FOSSEE/OpenPLC/OpenPLC_Atmega16/assets/openplc.png

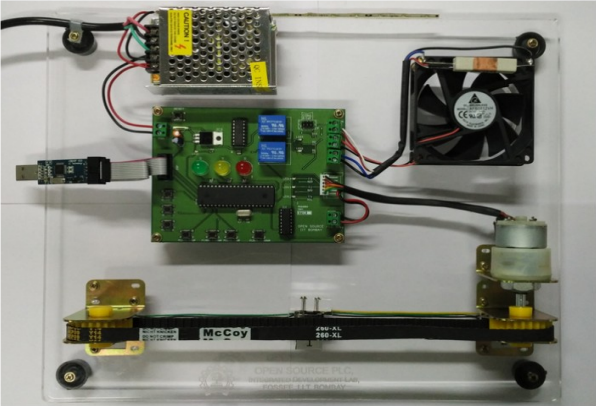
OpenPLC_Atmega16/assets/openplc.png
