FOSSEE/OpenPLC/OpenPLC_Atmega16/software/SoftImages/ldmicro.png

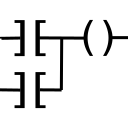
OpenPLC_Atmega16/software/SoftImages/ldmicro.png
