FOSSEE/OpenPLC/Resources/OpenPLCVersion1/OpenPLC.sch

## EAGLE design Resources/OpenPLCVersion1/OpenPLC.sch (2016-04-25)

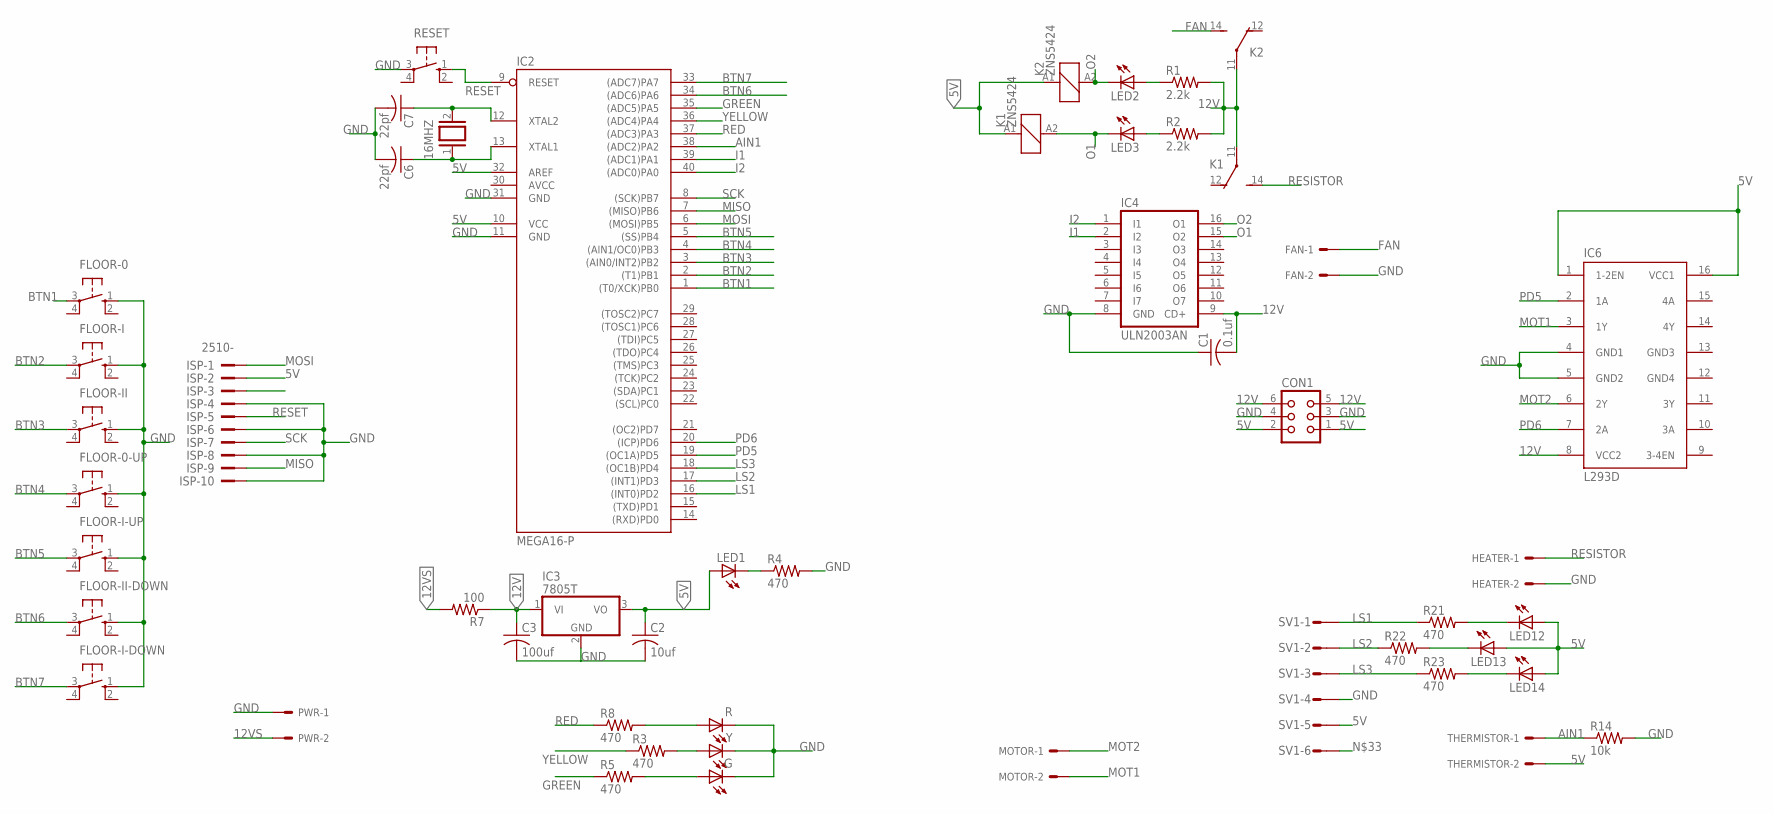
[picture p41: schematic OpenPLC.sch]

Parts:
16MHZ: XTAL/S; QS
C1: 0.1uf; C0805
C2: 10uf; C025-025X050
C3: 100uf; C025-025X050
C6, C7: 22pf; C0805
CON1: CON06
FAN: KK-156-2
FLOOR-0, FLOOR-0-UP: 10-XX; B3F-10XX
FLOOR-I: 10-XX; B3F-10XX
FLOOR-I-DOWN: 10-XX; B3F-10XX
FLOOR-I-UP: 10-XX; B3F-10XX
FLOOR-II: 10-XX; B3F-10XX
FLOOR-II-DOWN: 10-XX; B3F-10XX
G: LED10MM
HEATER: KK-156-2
IC2: MEGA16-P; DIL40
IC3: 7805T; TO220H
IC4: ULN2003AN; DIL16
IC6: L293D; DIL16
ISP: 2510-; PAK100/2500-10
K1, K2: ZNS5424; ZN5
LED1, LED2, LED3, LED12, LED13, LED14: LEDSML0805; SML0805
MOTOR: KK-156-2
PWR: KK-156-2
R: LED10MM
R1, R2: 2.2k; R0805
R3, R4, R5, R8, R21, R22, R23: 470; R0805
R7: 100; 0207/12
R14: 10k; R0805
RESET: 10-XX; B3F-10XX
SV1: L06P
THERMISTOR: KK-156-2
Y: LED10MM

Connections:
5V: C2.1, CON1.1, CON1.2, IC2.10 (VCC), IC2.32 (AREF), IC3.3 (VO), IC6.1 (1-2EN), IC6.16 (VCC1), ISP.2, K1.A1 (1), K2.A1 (1), LED1.A, LED12.A, LED13.A, LED14.A, SV1.5, THERMISTOR.2
12V: C1.2, C3.1, CON1.5, CON1.6, IC3.1 (VI), IC4.9 (CD+), IC6.8 (VCC2), K1.11, K2.11, R1.2, R2.2, R7.1
12VS: PWR.2, R7.2
AIN1: IC2.38 ((ADC2)PA2), R14.1, THERMISTOR.1
BTN1: FLOOR-0.3, IC2.1 ((T0/XCK)PB0)
BTN2: FLOOR-I.3, IC2.2 ((T1)PB1)
BTN3: FLOOR-II.3, IC2.3 ((AIN0/INT2)PB2)
BTN4: FLOOR-0-UP.3, IC2.4 ((AIN1/OC0)PB3)
BTN5: FLOOR-I-UP.3, IC2.5 ((SS)PB4)
BTN6: FLOOR-II-DOWN.3, IC2.34 ((ADC6)PA6)
BTN7: FLOOR-I-DOWN.3, IC2.33 ((ADC7)PA7)
FAN: FAN.1, K2.14 (S)
G: G.A, R5.2
GND: C1.1, C2.2, C3.2, C6.2, C7.2, CON1.3, CON1.4, FAN.2, FLOOR-0.1 (S), FLOOR-0-UP.1 (S), FLOOR-I.1 (S), FLOOR-I-DOWN.1 (S), FLOOR-I-UP.1 (S), FLOOR-II.1 (S), FLOOR-II-DOWN.1 (S), G.K (C), HEATER.2, IC2.11 (GND), IC2.31 (GND), IC3.2 (GND), IC4.8 (GND), IC6.4 (GND1), IC6.5 (GND2), ISP.4, ISP.6, ISP.8, ISP.10, PWR.1, R.K (C), R4.2, R14.2, RESET.3, SV1.4, Y.K (C)
GREEN: IC2.35 ((ADC5)PA5), R5.1
I1: IC2.39 ((ADC1)PA1), IC4.2 (I2)
I2: IC2.40 ((ADC0)PA0), IC4.1 (I1)
LS1: IC2.16 ((INT0)PD2), R21.1, SV1.1
LS2: IC2.17 ((INT1)PD3), R22.1, SV1.2
LS3: IC2.18 ((OC1B)PD4), R23.1, SV1.3
MISO: IC2.7 ((MISO)PB6), ISP.9
MOSI: IC2.6 ((MOSI)PB5), ISP.1
MOT1: IC6.3 (1Y), MOTOR.2
MOT2: IC6.6 (2Y), MOTOR.1
unnamed: LED1.C, R4.1
unnamed: LED2.A, R1.1
unnamed: LED3.A, R2.1
unnamed: LED12.C, R21.2
unnamed: LED13.C, R22.2
unnamed: LED14.C, R23.2
unnamed: 16MHZ.1, C6.1, IC2.13 (XTAL1)
unnamed: 16MHZ.2, C7.1, IC2.12 (XTAL2)
O1: IC4.15 (O2), K1.A2 (2), LED3.C
O2: IC4.16 (O1), K2.A2 (2), LED2.C
PD5: IC2.19 ((OC1A)PD5), IC6.2 (1A)
PD6: IC2.20 ((ICP)PD6), IC6.7 (2A)
R: R.A, R8.2
RED: IC2.37 ((ADC3)PA3), R8.1
RESET: IC2.9 (RESET), ISP.5, RESET.1 (S)
RESISTOR: HEATER.1, K1.14 (S)
SCK: IC2.8 ((SCK)PB7), ISP.7
Y: R3.2, Y.A
YELLOW: IC2.36 ((ADC4)PA4), R3.1
