FOSSEE/OpenPLC/Resources/OpenPLCVersion1/KiCAD_Files/OpenPLC_Kicad.sch

## KiCad design Resources/OpenPLCVersion1/KiCAD_Files/OpenPLC_Kicad.sch (2017-04-03)

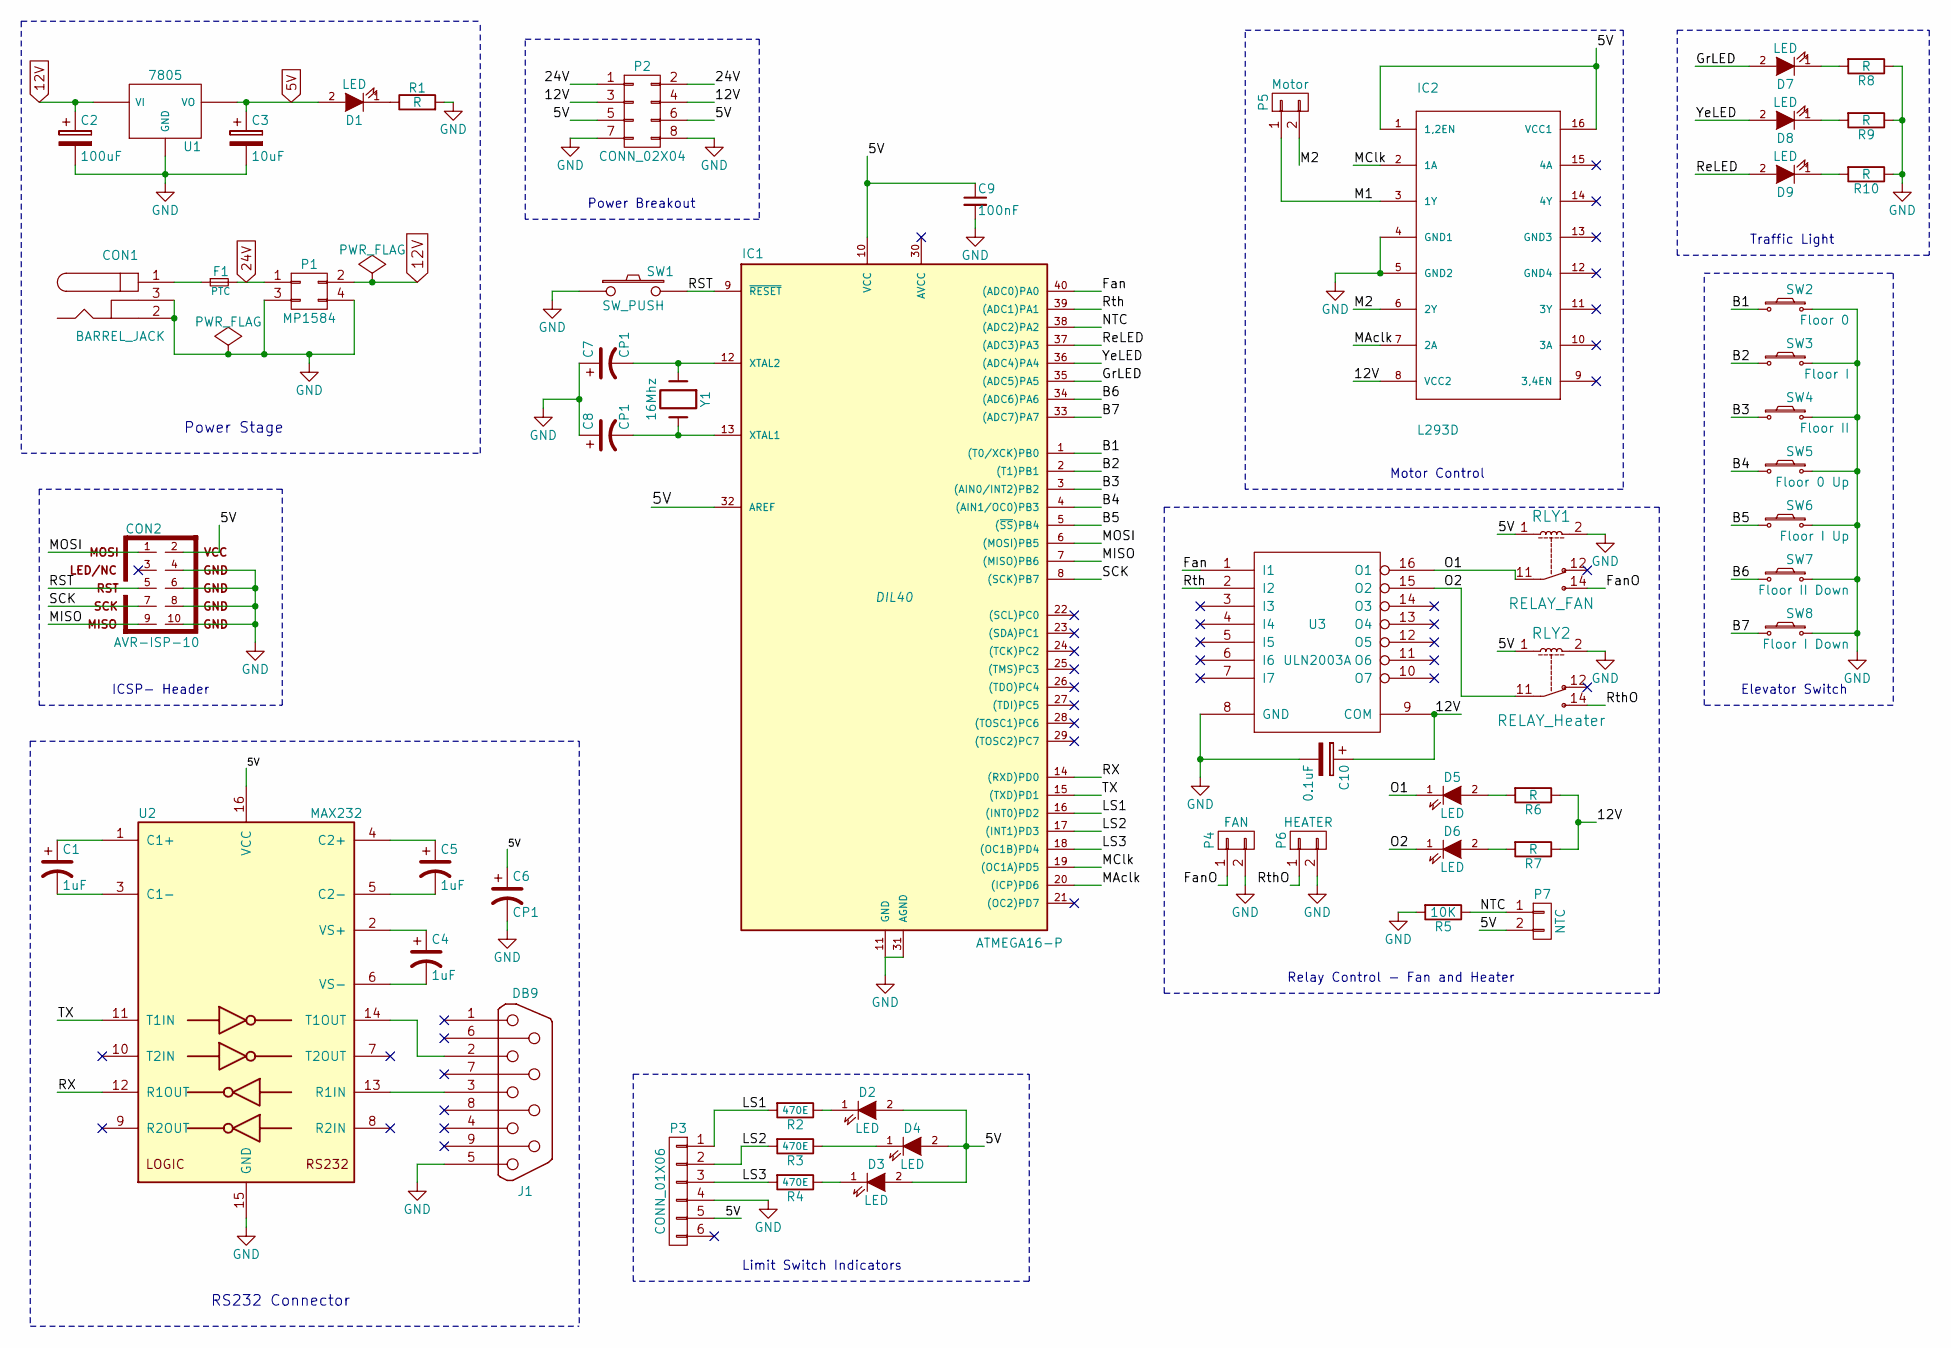
[picture p42: schematic OpenPLC_Kicad.sch]

Parts:
C1, C4, C5: 1uF
C2: 100uF
C3: 10uF
C6, C7, C8: CP1
C9: 100nF
C10: 0.1uF
CON1: BARREL_JACK
CON2: AVR-ISP-10
D1, D2, D3, D4, D5, D6, D7, D8, D9: LED
F1: PTC
IC1: ATMEGA16-P; DIL40
IC2: L293D; stepper drivers-DIL16
J1: DB9
P1: MP1584
P2: CONN_02X04
P3: CONN_01X06
P4: FAN
P5: Motor
P6: HEATER
P7: NTC
R1, R6, R7, R8, R9, R10: R
R2, R3, R4: 470E
R5: 10K
RLY1: RELAY_FAN
RLY2: RELAY_Heater
SW1: SW_PUSH
SW2: Floor 0
SW3: Floor I
SW4: Floor II
SW5: Floor 0 Up
SW6: Floor I Up
SW7: Floor II Down
SW8: Floor I Down
U1: 7805
U2: MAX232
U3: ULN2003A
Y1: 16Mhz

Connections:
5V: C3.1, C6.1, C9.1, CON2.2, D1.2 (A), D2.2 (A), D3.2 (A), D4.2 (A), IC1.10 (VCC), IC1.32 (AREF), IC2.1 (1,2EN), IC2.16 (VCC1), P2.5, P2.6, P3.5, P7.2, RLY1.1, RLY2.1, U1.VO, U2.16 (VCC)
12V: C2.1, C10.1, IC2.8 (VCC2), P1.2, P2.3, P2.4, R6.1, R7.1, U1.VI, U3.9 (COM)
24V: F1.2, P1.1, P2.1, P2.2
B1: IC1.1 ((T0/XCK)PB0), SW2.1
B2: IC1.2 ((T1)PB1), SW3.1
B3: IC1.3 ((AIN0/INT2)PB2), SW4.1
B4: IC1.4 ((AIN1/OC0)PB3), SW5.1
B5: IC1.5 ((~SS~)PB4), SW6.1
B6: IC1.34 ((ADC6)PA6), SW7.1
B7: IC1.33 ((ADC7)PA7), SW8.1
Fan: IC1.40 ((ADC0)PA0), U3.1 (I1)
FanO: P4.1, RLY1.14
GND: C2.2, C3.2, C6.2, C7.1, C8.1, C9.2, C10.2, CON1.2, CON1.3, CON2.4, CON2.6, CON2.8, CON2.10, IC1.11 (GND), IC1.31 (AGND), IC2.4 (GND1), IC2.5 (GND2), J1.5, P1.3, P1.4, P2.7, P2.8, P3.4, P4.2, P6.2, R1.2, R5.2, R8.1, R9.1, R10.1, RLY1.2, RLY2.2, SW1.1, SW2.2, SW3.2, SW4.2, SW5.2, SW6.2, SW7.2, SW8.2, U1.GND, U2.15 (GND), U3.8 (GND)
GrLED: D7.2 (A), IC1.35 ((ADC5)PA5)
LS1: IC1.16 ((INT0)PD2), P3.1, R2.2
LS2: IC1.17 ((INT1)PD3), P3.2, R3.2
LS3: IC1.18 ((OC1B)PD4), P3.3, R4.2
M1: IC2.3 (1Y), P5.1
M2: IC2.6 (2Y), P5.2
MAclk: IC1.20 ((ICP)PD6), IC2.7 (2A)
MClk: IC1.19 ((OC1A)PD5), IC2.2 (1A)
MISO: CON2.9, IC1.7 ((MISO)PB6)
MOSI: CON2.1, IC1.6 ((MOSI)PB5)
NTC: IC1.38 ((ADC2)PA2), P7.1, R5.1
unnamed: C1.1, U2.1 (C1+)
unnamed: C1.2, U2.3 (C1-)
unnamed: C4.1, U2.2 (VS+)
unnamed: C4.2, U2.6 (VS-)
unnamed: C5.1, U2.4 (C2+)
unnamed: C5.2, U2.5 (C2-)
unnamed: C7.2, IC1.12 (XTAL2), Y1.1
unnamed: C8.2, IC1.13 (XTAL1), Y1.2
unnamed: CON1.1, F1.1
unnamed: D1.1 (K), R1.1
unnamed: D2.1 (K), R2.1
unnamed: D3.1 (K), R4.1
unnamed: D4.1 (K), R3.1
unnamed: D5.2 (A), R6.2
unnamed: D6.2 (A), R7.2
unnamed: D7.1 (K), R8.2
unnamed: D8.1 (K), R9.2
unnamed: D9.1 (K), R10.2
unnamed: J1.2, U2.14 (T1OUT)
unnamed: J1.3, U2.13 (R1IN)
O1: D5.1 (K), RLY1.11, U3.16 (O1)
O2: D6.1 (K), RLY2.11, U3.15 (O2)
RST: CON2.5, IC1.9 (~RESET), SW1.2
RX: IC1.14 ((RXD)PD0), U2.12 (R1OUT)
ReLED: D9.2 (A), IC1.37 ((ADC3)PA3)
Rth: IC1.39 ((ADC1)PA1), U3.2 (I2)
RthO: P6.1, RLY2.14
SCK: CON2.7, IC1.8 ((SCK)PB7)
TX: IC1.15 ((TXD)PD1), U2.11 (T1IN)
YeLED: D8.2 (A), IC1.36 ((ADC4)PA4)

Notes on the sheet:
Power Stage
RS232 Connector
Traffic Light
ICSP- Header
Elevator Switch
Motor Control
Relay Control - Fan and Heater
Limit Switch Indicators
Power Breakout
